mForcella/rasBuoy/thesis figures/figure 2.4 solar_array.jpg

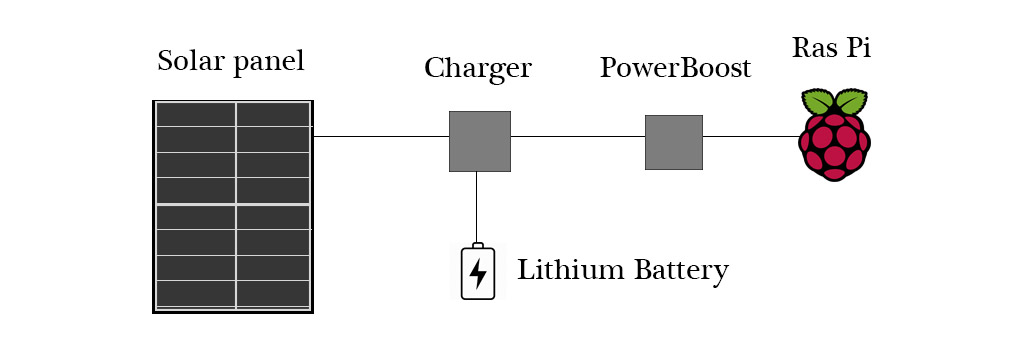
thesis figures/figure 2.4 solar_array.jpg
