mForcella/rasBuoy/python/xbee_test1.py

import serial

ser = serial.Serial('/dev/ttyAMA0', 9600)
string = 'Hello from yaface'
print 'Sending "%s"' % string
ser.write('%s\n' % string)

while True:
   incoming = ser.readline().strip()
   print 'Received %s' % incoming
   ser.write('RPi received: %s\n' % incoming)
